Wassim-eng/FE_WRO_BRAINIACS_2024/V-photos/Back.jpeg

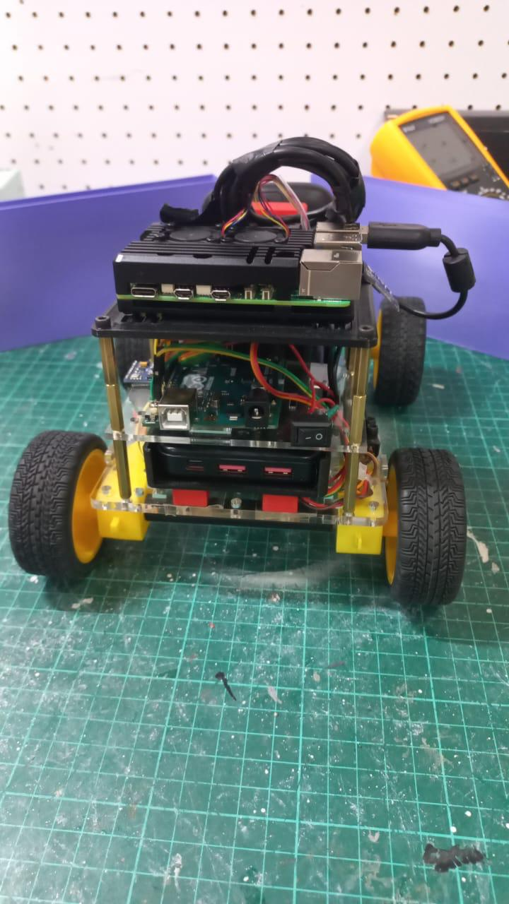
V-photos/Back.jpeg
