Wassim-eng/FE_WRO_BRAINIACS_2024/V-photos/Front.jpeg

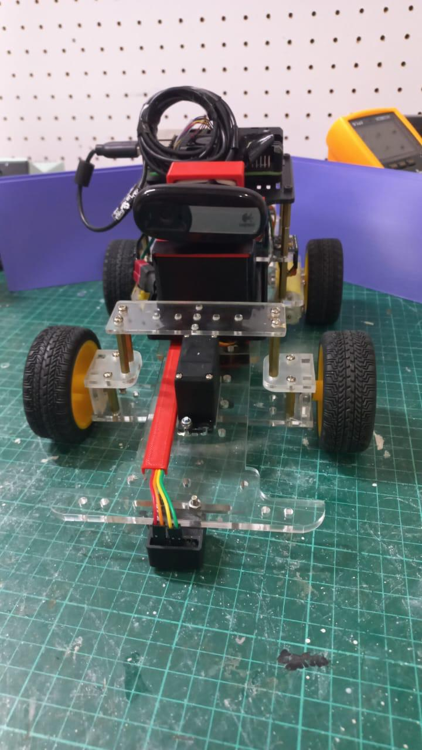
V-photos/Front.jpeg
