Wassim-eng/FE_WRO_BRAINIACS_2024/V-photos/Right.jpeg

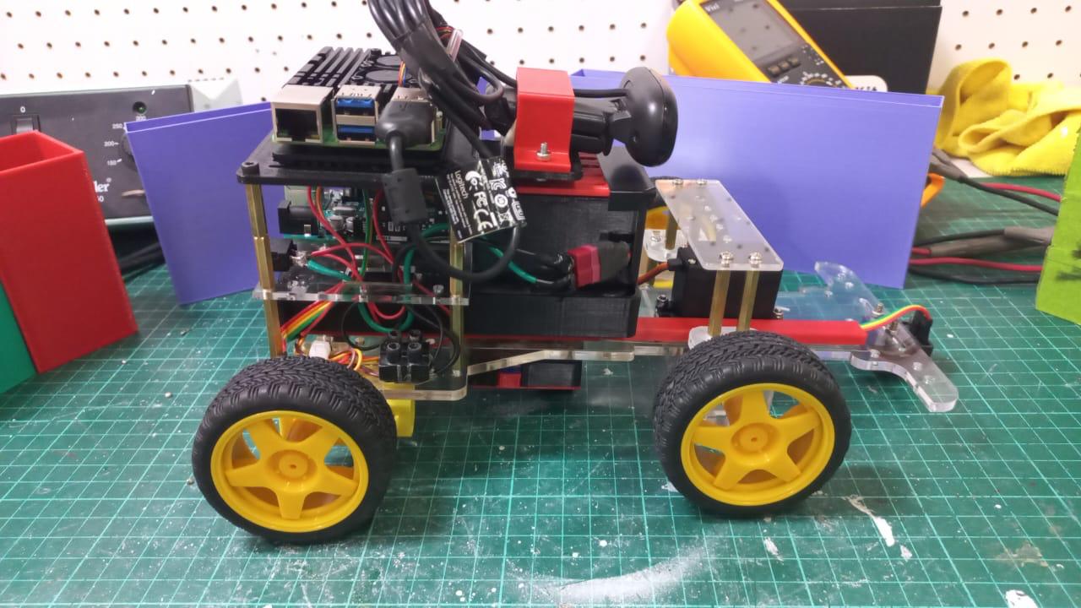
V-photos/Right.jpeg
