Wassim-eng/FE_WRO_BRAINIACS_2024/CAD models/Logitech c270 Assembly.SLDASM

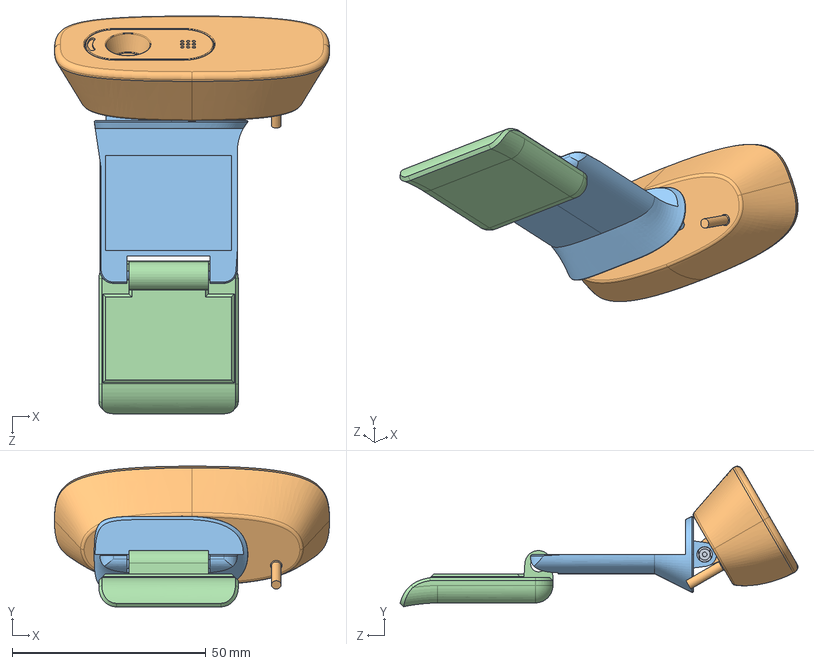
[picture p18: CAD file, 2024-07-12]
CAD models/Logitech c270 Assembly.SLDASM
71.0 x 36.3 x 102.7 mm
Logitech c270c
Logitech c270b
Logitech c270
Pin camera Mtg Plastic Logi c270
