Wassim-eng/FE_WRO_BRAINIACS_2024/CAD models/standoff_tall.SLDPRT

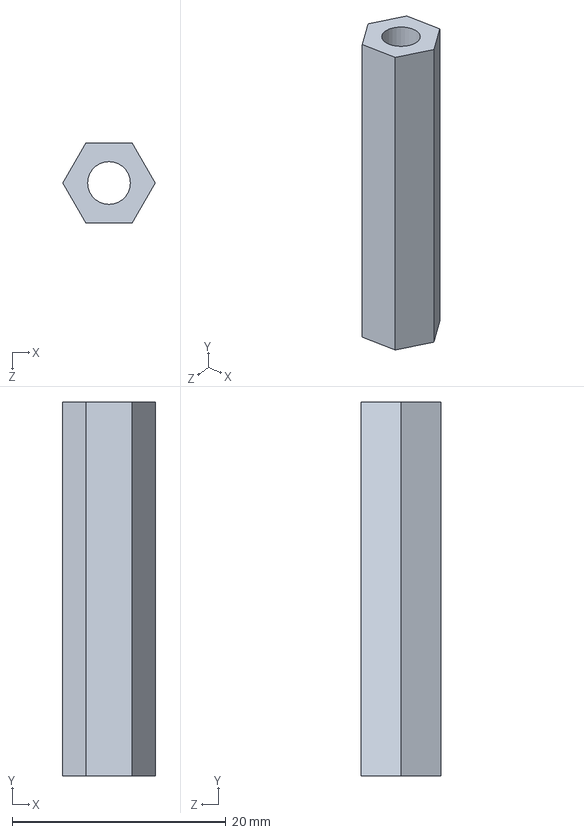
[picture p32: CAD file, 2024-07-12]
CAD models/standoff_tall.SLDPRT
8.66 x 35.0 x 7.50 mm
