Wassim-eng/FE_WRO_BRAINIACS_2024/CAD models/Mg995.SLDPRT

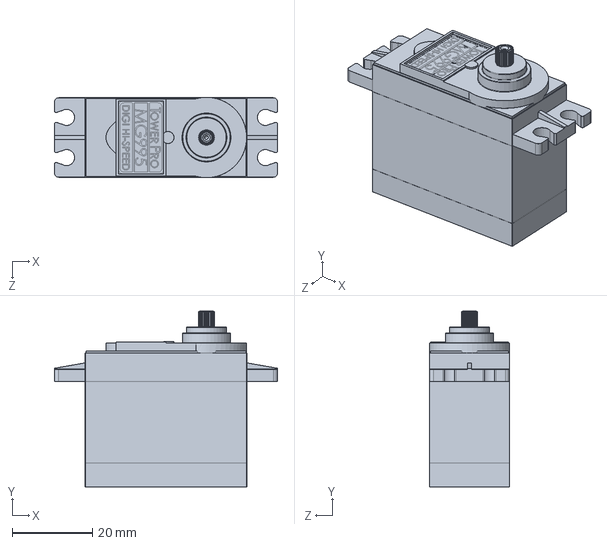
[picture p33: CAD file, 2024-07-12]
CAD models/Mg995.SLDPRT
55.5 x 43.8 x 20.0 mm
