Wassim-eng/FE_WRO_BRAINIACS_2024/CAD models/Boss-Extrude3.SLDPRT

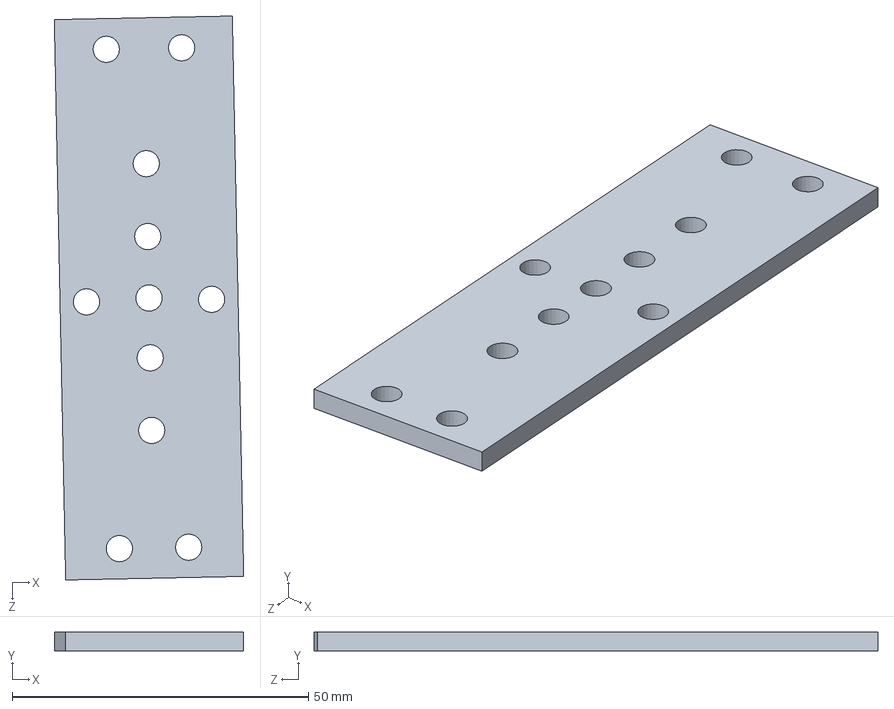
[picture p34: CAD file, 2024-07-12]
CAD models/Boss-Extrude3.SLDPRT
32.0 x 3.17 x 95.2 mm
