Wassim-eng/FE_WRO_BRAINIACS_2024/CAD models/Wheel D65x25.SLDPRT

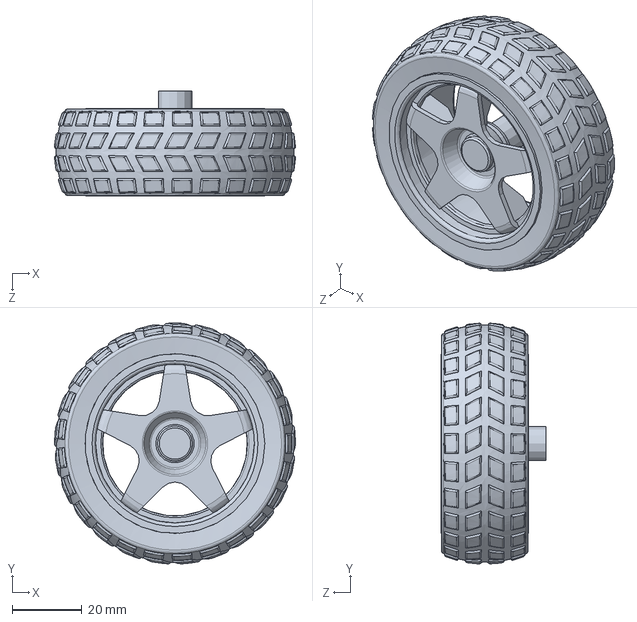
[picture p35: CAD file, 2024-07-12]
CAD models/Wheel D65x25.SLDPRT
68.9 x 68.8 x 30.0 mm
