Wassim-eng/FE_WRO_BRAINIACS_2024/CAD models/Split1[1].SLDPRT

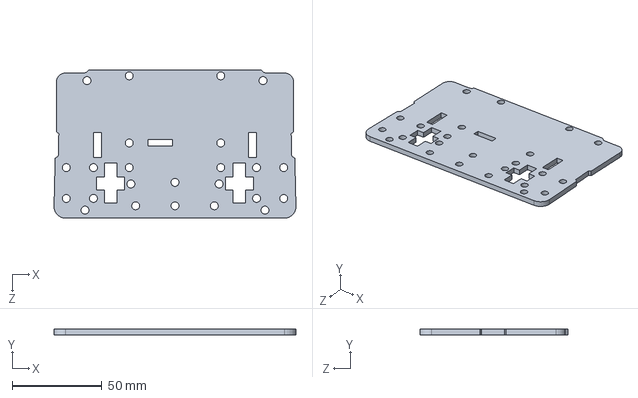
[picture p36: CAD file, 2024-07-12]
CAD models/Split1[1].SLDPRT
134.8 x 3.17 x 82.5 mm
