Wassim-eng/FE_WRO_BRAINIACS_2024/CAD models/Servo_MG995_Star_horn.SLDPRT

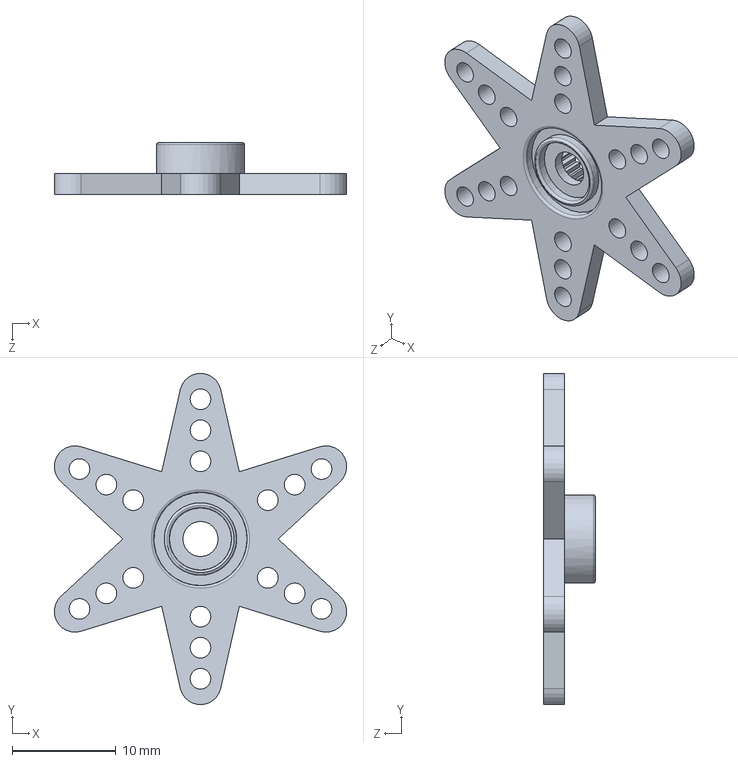
[picture p37: CAD file, 2024-07-12]
CAD models/Servo_MG995_Star_horn.SLDPRT
28.2 x 32.0 x 5.00 mm
