Wassim-eng/FE_WRO_BRAINIACS_2024/CAD models/Logitech c270.SLDPRT

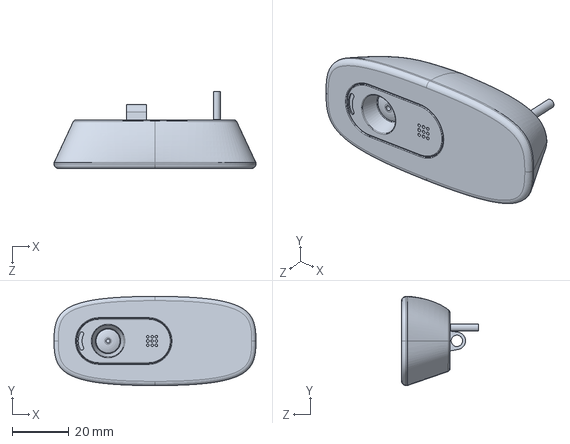
[picture p38: CAD file, 2024-07-12]
CAD models/Logitech c270.SLDPRT
71.0 x 31.4 x 27.0 mm
