Wassim-eng/FE_WRO_BRAINIACS_2024/CAD models/Boss-Extrude5.SLDPRT

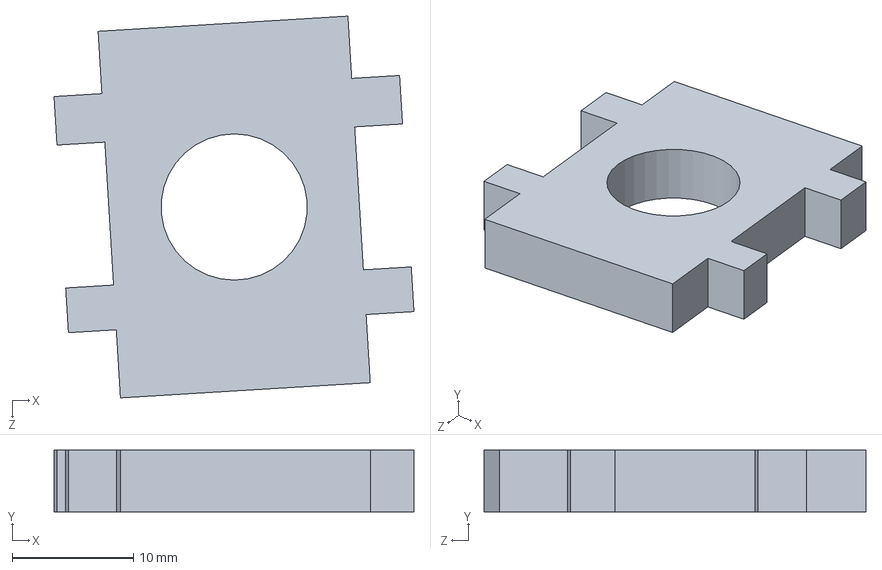
[picture p39: CAD file, 2024-07-12]
CAD models/Boss-Extrude5.SLDPRT
29.7 x 5.08 x 31.5 mm
