Wassim-eng/FE_WRO_BRAINIACS_2024/CAD models/Logitech c270c.SLDPRT

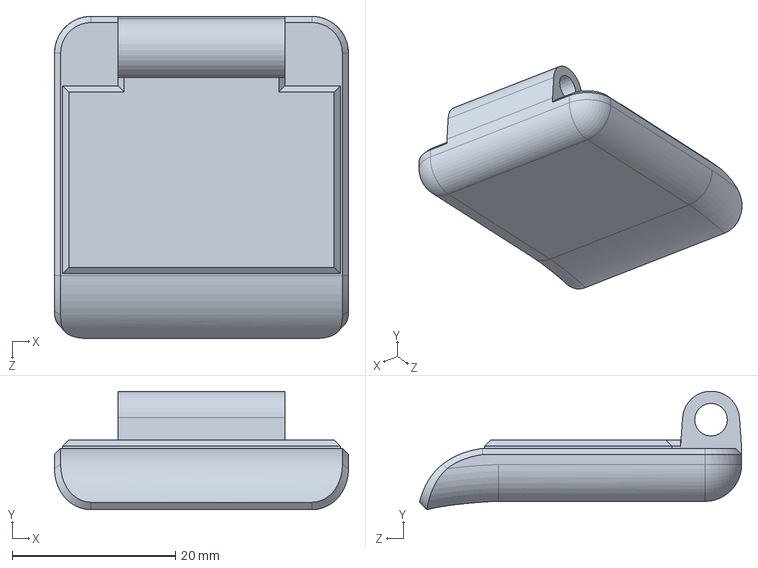
[picture p40: CAD file, 2024-07-12]
CAD models/Logitech c270c.SLDPRT
36.0 x 14.5 x 39.5 mm
